zitos97/Hypermobile-Joint-Protector/Media/Photos/sensorAndLilypadOnly.jpeg

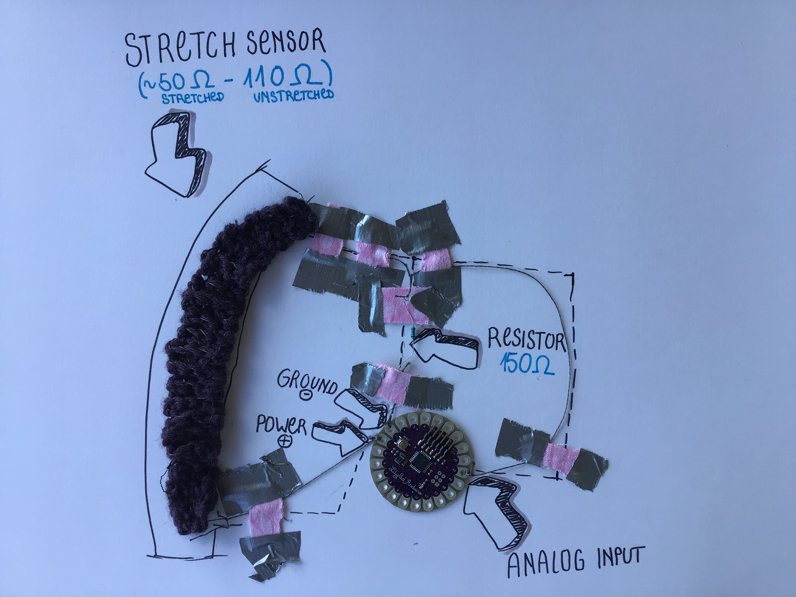
Media/Photos/sensorAndLilypadOnly.jpeg
