zitos97/Hypermobile-Joint-Protector/Media/Photos/TinkercadPrototypeCircuit.png

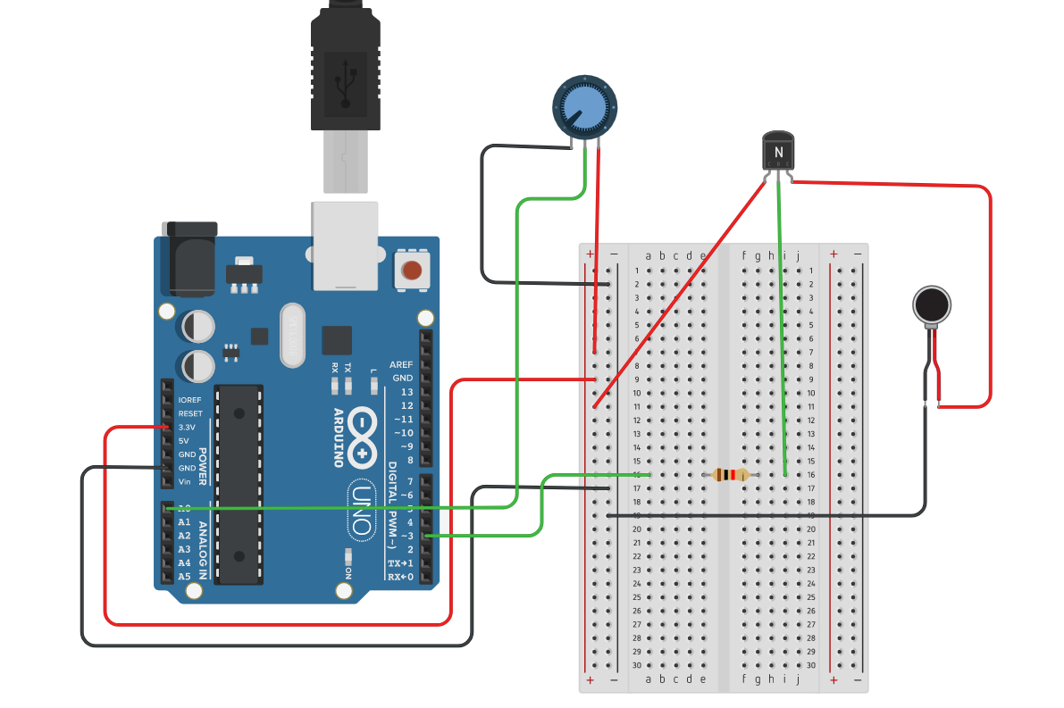
Media/Photos/TinkercadPrototypeCircuit.png
