zitos97/Hypermobile-Joint-Protector/Media/Photos/stretchSensorMaterials.png

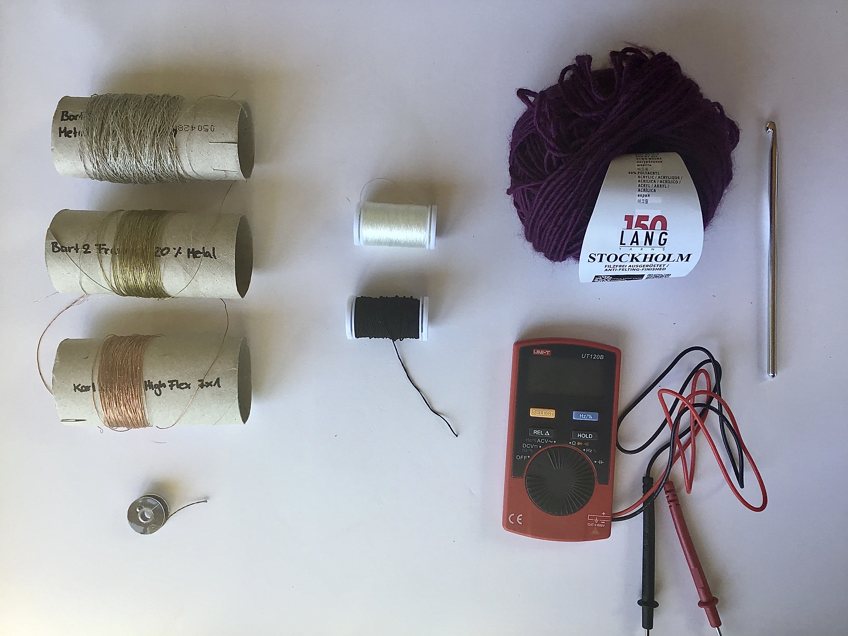
Media/Photos/stretchSensorMaterials.png
