zitos97/Hypermobile-Joint-Protector/Media/Photos/YarnEvaluation.png

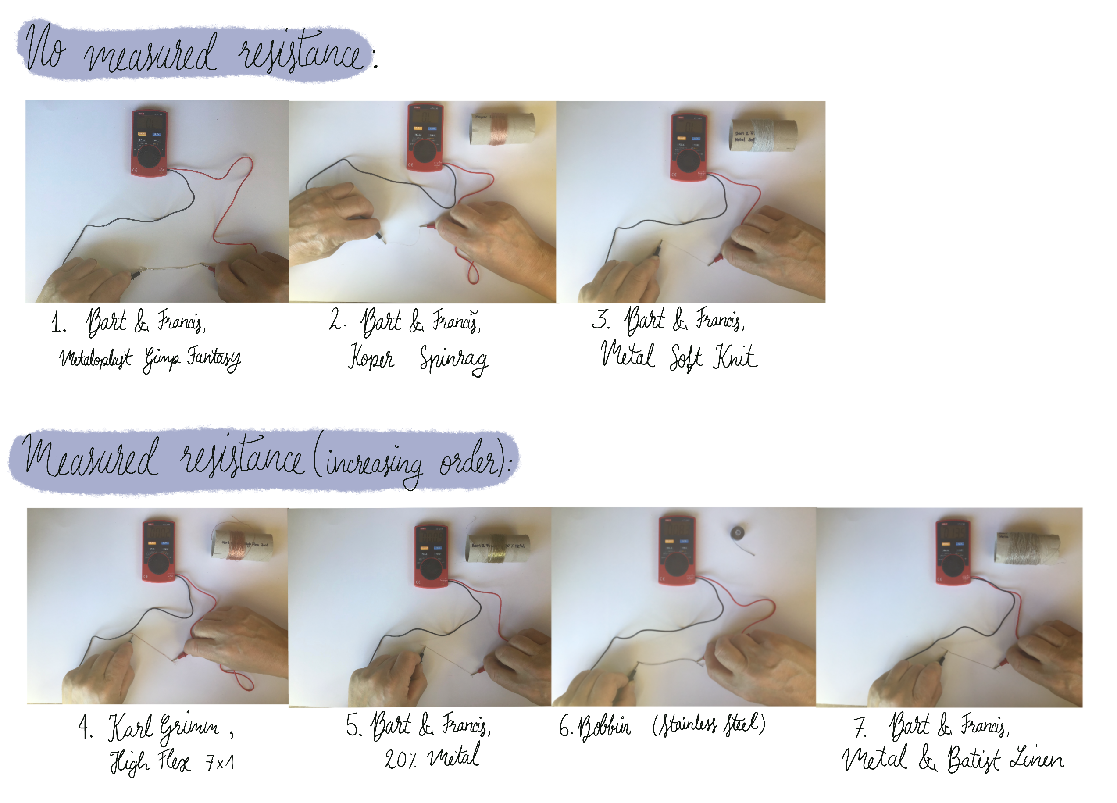
Media/Photos/YarnEvaluation.png
